vives-project-xp/Netwerkscanner/doc/img/sociale_media/binnenkant_netwerkscanner_dynamisch.png

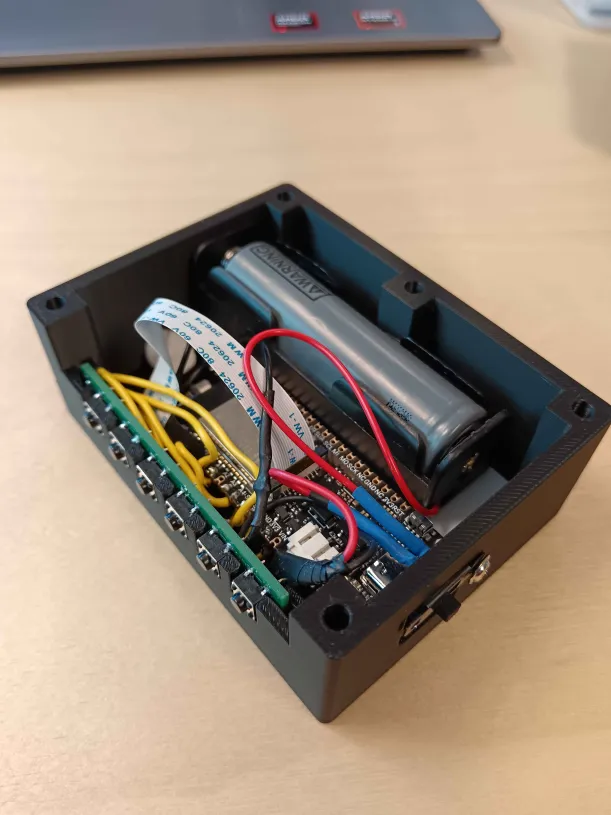
doc/img/sociale_media/binnenkant_netwerkscanner_dynamisch.png
