vives-project-xp/Netwerkscanner/doc/img/sociale_media/data.png

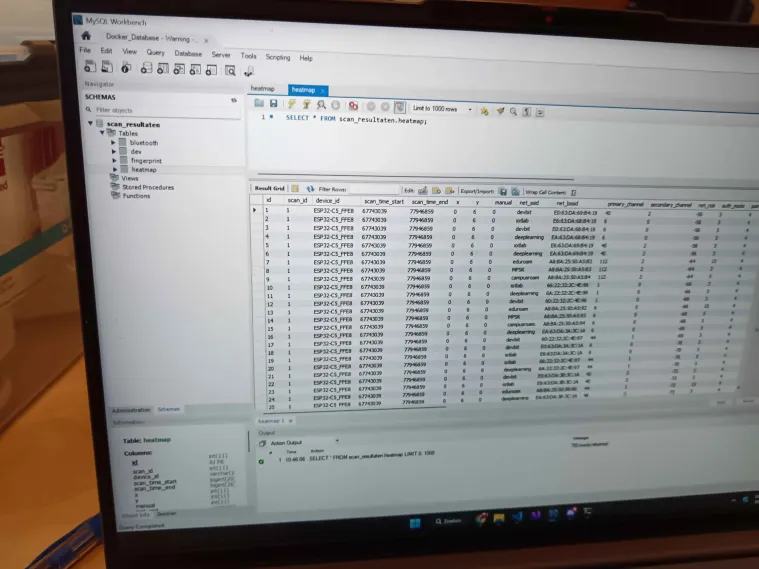
doc/img/sociale_media/data.png
