vives-project-xp/Netwerkscanner/doc/img/sociale_media/over_de_schouder_data.png

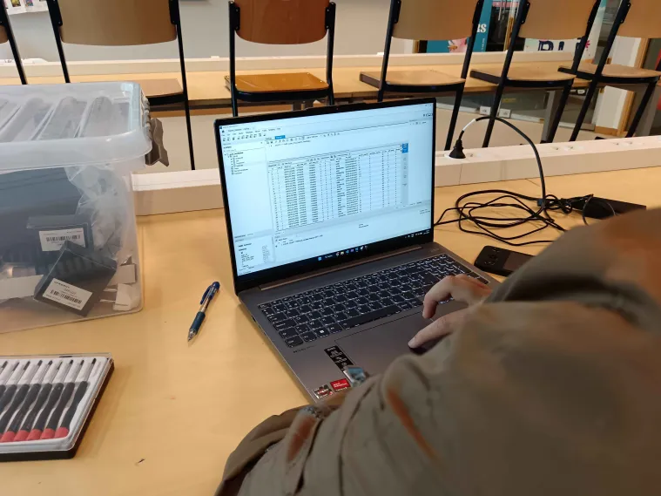
doc/img/sociale_media/over_de_schouder_data.png
