vives-project-xp/Netwerkscanner/doc/positiebepaling_ideas/3d_weergave.png

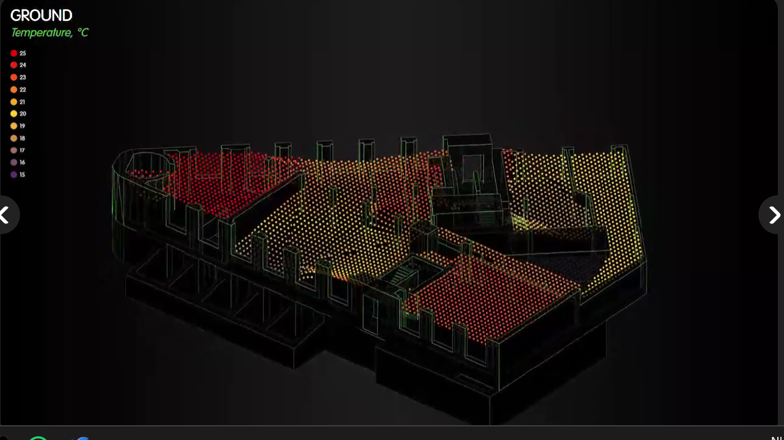
doc/positiebepaling_ideas/3d_weergave.png
