vives-project-xp/Netwerkscanner/doc/positiebepaling_ideas/precies_nauwkeurig.png

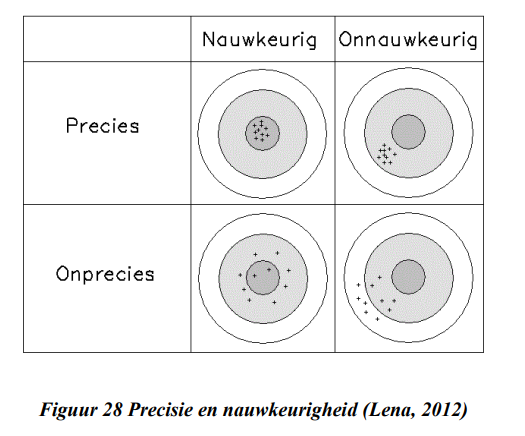
doc/positiebepaling_ideas/precies_nauwkeurig.png
