vives-project-xp/Netwerkscanner/doc/varia/assets/image.png

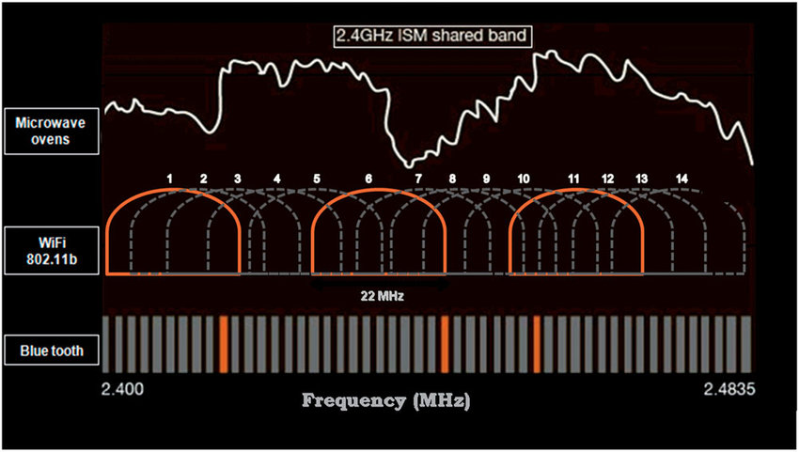
doc/varia/assets/image.png
