vives-project-xp/Netwerkscanner/doc/varia/power delivery/power delivery.drawio.png

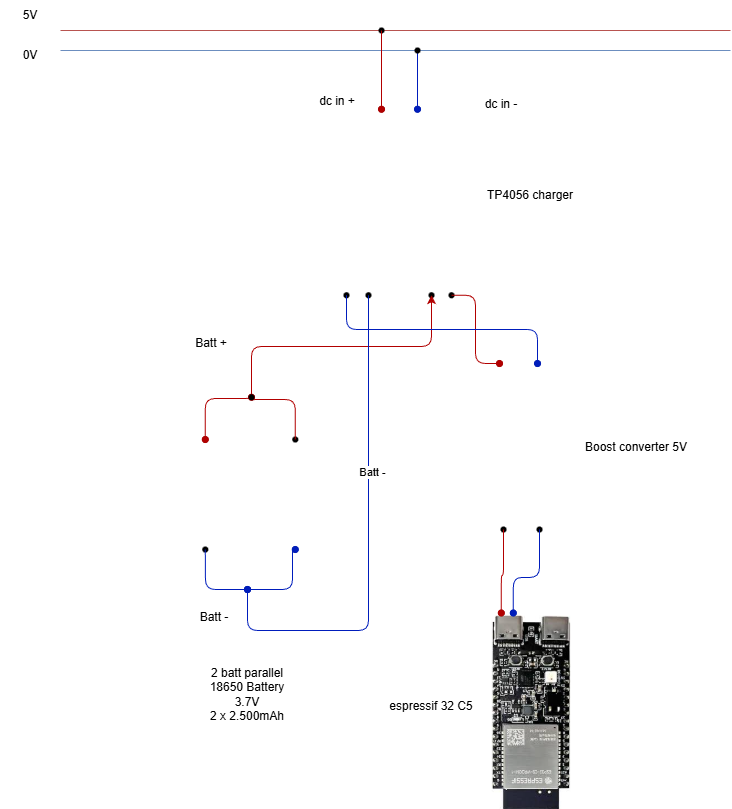
doc/varia/power delivery/power delivery.drawio.png
