vives-project-xp/Netwerkscanner/doc/varia/power delivery/power delivery.png

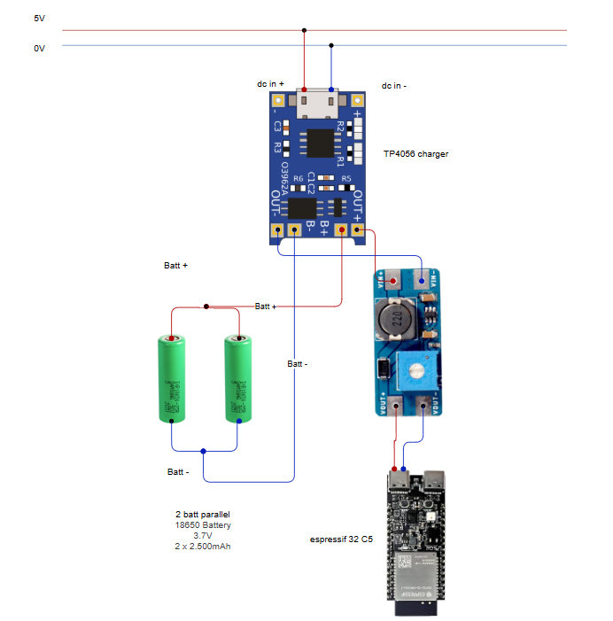
doc/varia/power delivery/power delivery.png
