vives-project-xp/Netwerkscanner/doc/varia/power delivery/TP4056.png

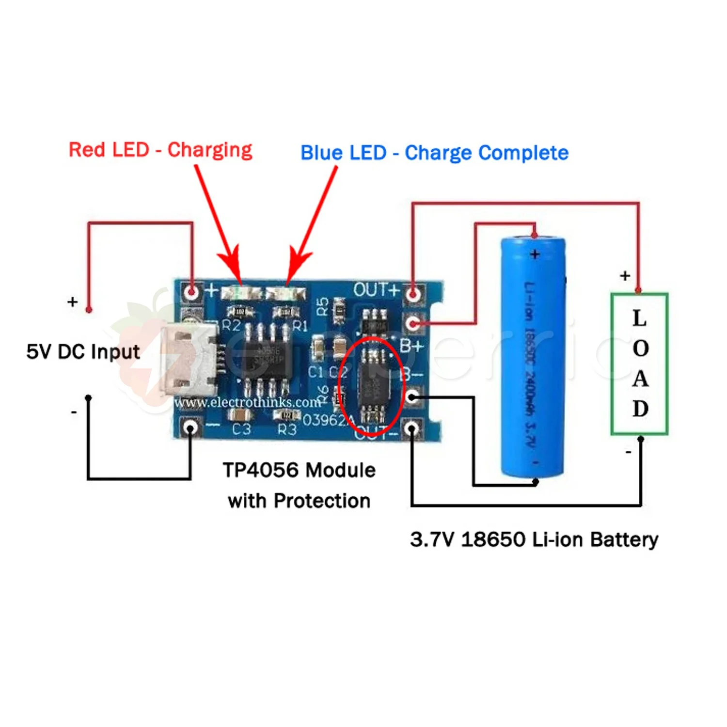
doc/varia/power delivery/TP4056.png
