vives-project-xp/Netwerkscanner/software/wifi-scannen-positiebepaling/flow_chart.png

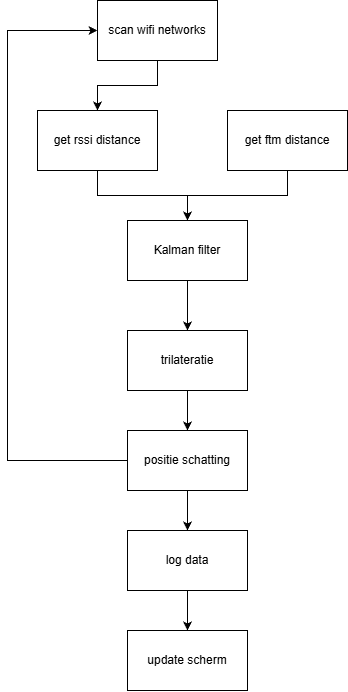
software/wifi-scannen-positiebepaling/flow_chart.png
