vives-project-xp/Netwerkscanner/software/wifi-scannen-positiebepaling/src/access_point.cpp

#include <Arduino.h>
#include <vector>
#include <String>

#include "debug.h"
#include "access_point.h"


float x;
float y;
float z;
float RMSE; // root mean squared error
String macPrefix;
std::vector<int> RSSI;
std::vector<String> SSID;
std::vector<String> BSSID;
// Constructor
AccessPoint::AccessPoint() {}
AccessPoint::AccessPoint(float xVal, float yVal, String macPrefix, float RMSE)
{
    x = xVal;
    y = yVal;
    z = 0.0f;
    this->macPrefix = macPrefix;
    this->RMSE = RMSE;
}

// Getters
float AccessPoint::GetX() const
{
    return x;
}

float AccessPoint::GetY() const
{
    return y;
}

float AccessPoint::GetZ() const
{
    return z;
}

float AccessPoint::GetRMSE() const
{
    return RMSE;
}

String AccessPoint::GetMacPrefix() const
{
    return macPrefix;
}

// Setters
void AccessPoint::SetX(float xVal)
{
    x = xVal;
}

void AccessPoint::SetY(float yVal)
{
    y = yVal;
}

void AccessPoint::SetPos(float xVal, float yVal)
{
    x = xVal;
    y = yVal;
}

void AccessPoint::SetRMSE(float rmse)
{
    RMSE = rmse;
}

void AccessPoint::AddRSSI(int rssi)
{
    RSSI.push_back(rssi);
}

void AccessPoint::AddSSID(String ssid)
{
    SSID.push_back(ssid);
}

void AccessPoint::AddBSSID(String bssid)
{
    BSSID.push_back(bssid);
}

// Functies
float AccessPoint::GetAverageRssi() const
{
    size_t vectorSize = RSSI.size();
    if (vectorSize == 0)
    {
        debugln("vector rssi was leeg");
        return -1;
    }

    int sum = 0;
    for (int val : RSSI)
    {
        sum += val;
    }
    return (float)sum / vectorSize;
}

float AccessPoint::RssiToMeter(float rssi) const
{
    const int rssiOp1Meter = -34;          // rssi waarde op 1 meter
    const float propagationConstant = 3.2; // hoe goed kan het signaal in de ruimte bewegen.//[2-4]
    return powf(10, (rssiOp1Meter - rssi) / (10.0f * propagationConstant));
}

void AccessPoint::ResetVectors()
{
    RSSI.clear();
    SSID.clear();
    BSSID.clear();
}
