vives-project-xp/Netwerkscanner/software/wifi-scannen-positiebepaling/src/non_linear_least_squares.h

#ifndef NON_LINEAR_LEAST_SQUARES
#define NON_LINEAR_LEAST_SQUARES

#include <vector>
struct Punt
{
    double x, y;
};
int TestNonLinearLeastSquares(const std::vector<AccessPoint> &aps1,
                                  const std::vector<double> &distances1);
int TestNonLinearLeastSquares();
#endif
