vives-project-xp/Netwerkscanner/software/wifi-scannen-positiebepaling/src/trilateratie_n_points.h

#ifndef TRILATERATIE_N_POINTS
#define TRILATERATIE_N_POINTS

#include "access_point.h"

struct TrilaterationResult
{
    float x;
    float y;
    float RMSE;
};

void TestTrilateratieLeastSquares();
TrilaterationResult TrilateratieLeastSquares(const std::vector<AccessPoint> &aps,
                                             const std::vector<double> &distances);

#endif
