vives-project-xp/Netwerkscanner/software/Netwerkscanner/main/wifi_key_example.h

#ifndef WIFI_KEY
#define WIFI_KEY
//rename naar wifi_key.h

#define WIFI_SSID_EXAMPLE_0 "wifiSSID"
#define WIFI_PASSWORD_EXAMPLE_0 "Password"
#define WIFI_SSID_EXAMPLE_1 "wifiSSID2"
#define WIFI_PASSWORD_EXAMPLE_1 "Password"

#define SERVER_IP "10.23.10.24"
#define SERVER_PORT 8081
static const char* serverUrl = "http://10.23.10.24:8081/upload";
#endif
