vives-project-xp/Netwerkscanner/software/wifi-scannen-positiebepaling/src/test1_2_3.cpp

#include <Arduino.h>
#include <WiFi.h>
/*
 *  ESP32 WiFi Scanner Example. Examples > WiFi > WiFiScan
 *  Full Tutorial @
 * https://deepbluembedded.com/esp32-wifi-library-examples-tutorial-arduino/
 */

#include "test1_2_3.h"

void Test1_2() // vind alle netwerken.
{
  Serial.println("Scan start");

  // WiFi.scanNetworks will return the number of networks found.
  // standaard int n = WiFi.scanNetworks(false, true, true, 100);
  int n = WiFi.scanNetworks(false, true, true, 100);
  Serial.println("Scan done");
  if (n == 0)
  {
    Serial.println("no networks found");
  }
  else
  {
    Serial.print(n);
    Serial.println(" networks found");
    Serial.println(
        "Nr | SSID                             | RSSI |  | BSSID                    | CH | Encryption");
    for (int i = 0; i < n; ++i)
    {
      // Print SSID and RSSI for each network found
      Serial.printf("%2d", i + 1);
      Serial.print(" | ");

      Serial.printf("%-32.32s", WiFi.SSID(i).c_str());
      Serial.print(" | ");

      Serial.printf("%4d", WiFi.RSSI(i));
      Serial.print(" | ");

      Serial.print(" | BSSID: ");
      Serial.print(WiFi.BSSIDstr(i));
      Serial.print(" | ");

      Serial.printf("%2d", WiFi.channel(i));
      Serial.print(" | ");

      switch (WiFi.encryptionType(i))
      {
      case WIFI_AUTH_OPEN:
        Serial.print("open");
        break;
      case WIFI_AUTH_WEP:
        Serial.print("WEP");
        break;
      case WIFI_AUTH_WPA_PSK:
        Serial.print("WPA");
        break;
      case WIFI_AUTH_WPA2_PSK:
        Serial.print("WPA2");
        break;
      case WIFI_AUTH_WPA_WPA2_PSK:
        Serial.print("WPA+WPA2");
        break;
      case WIFI_AUTH_WPA2_ENTERPRISE:
        Serial.print("WPA2-EAP");
        break;
      case WIFI_AUTH_WPA3_PSK:
        Serial.print("WPA3");
        break;
      case WIFI_AUTH_WPA2_WPA3_PSK:
        Serial.print("WPA2+WPA3");
        break;
      case WIFI_AUTH_WAPI_PSK:
        Serial.print("WAPI");
        break;
      default:
        Serial.print("unknown");
      }
      Serial.println();
    }
  }
  Serial.println("");

  // Delete the scan result to free memory for code below.
  WiFi.scanDelete();

  // Wait a bit before scanning again.
}

void Test3() // snelheid test
{

  const int scans = 10;
  unsigned int timeStart = 0;
  unsigned int timeStop = 0;
  timeStart = millis();
  for (int i = 0; i < scans; i++)
  {
    WiFi.scanNetworks(false, true, false, 80); // online repo kiest ook 80ms per channel
  }
  timeStop = millis();
  Serial.println("gemiddelde voor 1 scan = " + String((timeStop - timeStart) / scans));
}
